bman12three4/super6502/hw/efinix_fpga/src/super6502.sv

module super6502
(
    input logic i_sysclk,       // Controller Clock (100MHz)
    input logic i_sdrclk,       // t_su and t_wd clock (200MHz)
    input logic i_tACclk,       // t_ac clock (200MHz)

    input [7:0] cpu_data_in,
    input cpu_sync,
    input cpu_rwb,
    input pll_in,
    input button_reset,
    input pll_cpu_locked,
    input clk_50,
    input clk_cpu,
    input logic [15:0] cpu_addr,
    output logic [7:0] cpu_data_out,
    output logic [7:0] cpu_data_oe,
    output logic cpu_irqb,
    output logic cpu_nmib,
    output logic cpu_rdy,
    output logic cpu_resb,
    output logic pll_cpu_reset,
    output logic cpu_phi2,

    output logic [7:0] leds,

    output logic o_pll_reset,
    output	logic o_sdr_CKE,
    output	logic o_sdr_n_CS,
    output	logic o_sdr_n_WE,
    output	logic o_sdr_n_RAS,
    output	logic o_sdr_n_CAS,
    output	logic [1:0] o_sdr_BA,
    output	logic [12:0] o_sdr_ADDR,
    input	logic [15:0] i_sdr_DATA,
    output	logic [15:0] o_sdr_DATA,
    output	logic [15:0] o_sdr_DATA_oe,
    output	logic [1:0] o_sdr_DQM,

    input uart_rx,
    output uart_tx,

    output sd_cs,
    output spi_clk,
    output spi_mosi,
    
    input spi_miso
);

assign pll_cpu_reset = '1;
assign o_pll_reset = '1;

assign cpu_data_oe = {8{cpu_rwb}};
assign cpu_nmib = '1;

logic w_wait;
assign cpu_rdy = ~w_wait;

assign cpu_phi2 = clk_cpu;

logic w_sdr_init_done;

always @(posedge clk_cpu) begin
    if (button_reset == '0) begin
        cpu_resb <= '0;
    end 
    else begin
        if (cpu_resb == '0 && w_sdr_init_done) begin
            cpu_resb <= '1;
        end
    end
end


logic w_rtc_irq;

logic w_mapper_cs;

logic w_rom_cs;
logic w_leds_cs;
logic w_sdram_cs;
logic w_timer_cs;
logic w_multiplier_cs;
logic w_divider_cs;
logic w_uart_cs;
logic w_spi_cs;
logic w_irq_cs;
logic w_rtc_cs;


logic [7:0] w_rom_data_out;
logic [7:0] w_leds_data_out;
logic [7:0] w_timer_data_out;
logic [7:0] w_multiplier_data_out;
logic [7:0] w_divider_data_out;
logic [7:0] w_uart_data_out;
logic [7:0] w_spi_data_out;
logic [7:0] w_irq_data_out;
logic [7:0] w_rtc_data_out;
logic [7:0] w_sdram_data_out;

logic [24:0] w_mapped_addr;

always_comb begin
    w_mapper_cs = cpu_addr >= 16'h200 && cpu_addr <= 16'h21f;

    w_rom_cs = w_mapped_addr >= 16'hf000 && w_mapped_addr <= 16'hffff;
    w_rtc_cs = w_mapped_addr >= 16'heffe && w_mapped_addr <= 16'hefff;
    w_irq_cs = w_mapped_addr >= 16'heffc && w_mapped_addr <= 16'heffd;
    w_timer_cs = w_mapped_addr >= 16'heff8 && w_mapped_addr <= 16'heffb;
    w_multiplier_cs = w_mapped_addr >= 16'heff0 && w_mapped_addr <= 16'heff7;
    w_divider_cs = w_mapped_addr >= 16'hefe8 && w_mapped_addr <= 16'hefef;
    w_uart_cs = w_mapped_addr >= 16'hefe6 && w_mapped_addr <= 16'hefe7;
    w_spi_cs = w_mapped_addr >= 16'hefd8 && w_mapped_addr <= 16'hefdb;
    w_leds_cs = w_mapped_addr == 16'hefd7;
    
    w_sdram_cs = ~(
        w_rom_cs | 
        w_timer_cs | 
        w_multiplier_cs | 
        w_divider_cs | 
        w_uart_cs | 
        w_spi_cs |
        w_leds_cs |
        w_irq_cs |
        w_rtc_cs
    );


    if (w_rom_cs)
        cpu_data_out = w_rom_data_out;
    else if (w_mapper_cs)
        cpu_data_out = w_mapper_data_out;
    else if (w_leds_cs)
        cpu_data_out = w_leds_data_out;
    else if (w_timer_cs)
        cpu_data_out = w_timer_data_out;
    else if (w_multiplier_cs)
        cpu_data_out = w_multiplier_data_out;
    else if (w_divider_cs)
        cpu_data_out = w_divider_data_out;
    else if (w_uart_cs)
        cpu_data_out = w_uart_data_out;
    else if (w_spi_cs)
        cpu_data_out = w_spi_data_out;
    else if (w_irq_cs)
        cpu_data_out = w_irq_data_out;
    else if (w_rtc_cs)
        cpu_data_out = w_rtc_data_out;
    else if (w_sdram_cs)
        cpu_data_out = w_sdram_data_out;
    else
        cpu_data_out = 'x;
end

rom #(.DATA_WIDTH(8), .ADDR_WIDTH(12)) u_rom(
    .addr(w_mapped_addr[11:0]),
    .clk(clk_cpu),
    .data(w_rom_data_out)
);

logic w_irq;
assign cpu_irqb = ~w_irq;
logic [127:0] w_int_in;

assign w_int_in[127:2] = 0;

interrupt_controller u_interrupt_controller(
    .clk(clk_cpu),
    .reset(~cpu_resb),
    .i_data(cpu_data_in),
    .o_data(w_irq_data_out),
    .addr(w_mapped_addr[0]),
    .cs(w_irq_cs),
    .rwb(cpu_rwb),
    .int_in(w_int_in),
    .int_out(w_irq)
);

leds u_leds(
    .clk(clk_cpu),
    .i_data(cpu_data_in),
    .o_data(w_leds_data_out),
    .cs(w_leds_cs),
    .rwb(cpu_rwb),
    .o_leds(leds)
);

logic w_timer_irqb;

timer u_timer(
    .clk(clk_cpu),
    .reset(~cpu_resb),
    .i_data(cpu_data_in),
    .o_data(w_timer_data_out),
    .cs(w_timer_cs),
    .rwb(cpu_rwb),
    .addr(w_mapped_addr[1:0]),
    .irqb(w_timer_irqb)
);

mapper u_mapper(
    .i_reset(~cpu_resb),
    .i_clk(clk_cpu),
    .i_clk50(clk_50),
    .i_clk100(i_sysclk),
    .i_cs(w_mapper_cs),
    .i_we(~cpu_rwb),
    .i_data(cpu_data_in),
    .o_data(w_mapper_data_out),
    .i_cpu_addr(cpu_addr),
    .o_mapped_addr(w_mapped_addr)
);

multiplier u_multiplier(
    .clk(clk_cpu),
    .reset(~cpu_resb),
    .i_data(cpu_data_in),
    .o_data(w_multiplier_data_out),
    .cs(w_multiplier_cs),
    .rwb(cpu_rwb),
    .addr(w_mapped_addr[2:0])
);

divider_wrapper u_divider(
    .clk(clk_cpu),
    .divclk(clk_50),
    .reset(~cpu_resb),
    .i_data(cpu_data_in),
    .o_data(w_divider_data_out),
    .cs(w_divider_cs),
    .rwb(cpu_rwb),
    .addr(w_mapped_addr[2:0])
);

logic w_uart_irq;

uart_wrapper u_uart(
    .clk(clk_cpu),
    .clk_50(clk_50),
    .reset(~cpu_resb),
    .i_data(cpu_data_in),
    .o_data(w_uart_data_out),
    .cs(w_uart_cs),
    .rwb(cpu_rwb),
    .addr(w_mapped_addr[0]),
    .rx_i(uart_rx),
    .tx_o(uart_tx),
    .irq(w_uart_irq)
);

assign w_int_in[1] = w_uart_irq;

spi_controller spi_controller(
    .i_clk_cpu(clk_cpu),
    .i_clk_50(clk_50),
    .i_rst(~cpu_resb),
    .i_cs(w_spi_cs),
    .i_rwb(cpu_rwb),
    .i_addr(w_mapped_addr[1:0]),
    .i_data(cpu_data_in),
    .o_data(w_spi_data_out),

    .o_spi_cs(sd_cs),
    .o_spi_clk(spi_clk),
    .o_spi_mosi(spi_mosi),
    .i_spi_miso(spi_miso)
);


sdram_adapter u_sdram_adapter(
    .i_cpuclk(clk_cpu),
    .i_arst(~button_reset),
    .i_sysclk(i_sysclk),
    .i_sdrclk(i_sdrclk),
    .i_tACclk(i_tACclk),

    .i_cs(w_sdram_cs),
    .i_rwb(cpu_rwb),

    .i_addr(w_mapped_addr),
    .i_data(cpu_data_in),
    .o_data(w_sdram_data_out),

    .o_sdr_init_done(w_sdr_init_done),
    .o_wait(w_wait),

    .o_sdr_CKE(o_sdr_CKE),
    .o_sdr_n_CS(o_sdr_n_CS),
    .o_sdr_n_RAS(o_sdr_n_RAS),
    .o_sdr_n_CAS(o_sdr_n_CAS),
    .o_sdr_n_WE(o_sdr_n_WE),
    .o_sdr_BA(o_sdr_BA),
    .o_sdr_ADDR(o_sdr_ADDR),
    .o_sdr_DATA(o_sdr_DATA),
    .o_sdr_DATA_oe(o_sdr_DATA_oe),
    .i_sdr_DATA(i_sdr_DATA),
    .o_sdr_DQM(o_sdr_DQM)
);

rtc u_rtc(
    .clk(clk_cpu),
    .reset(~cpu_resb),
    .rwb(cpu_rwb),
    .cs(w_rtc_cs),
    .addr(w_mapped_addr[0]),
    .i_data(cpu_data_in),
    .o_data(w_rtc_data_out),
    .irq(w_rtc_irq)
);

assign w_int_in[0] = w_rtc_irq;

endmodule
