bman12three4/super6502/sw/bios/devices/interrupt.h

#ifndef _INTERRUPT_H
#define _INTERRUPT_H

#include <stdint.h>

#define BUTTON  (1 << 0)
#define UART    (1 << 1)

void irq_int();
void nmi_int();

uint8_t irq_get_status();
void irq_set_status(uint8_t);

#endif
